promesoft/KicadJE_uP_DAC/RevA/KicadJE_uP_DAC_Top3.png

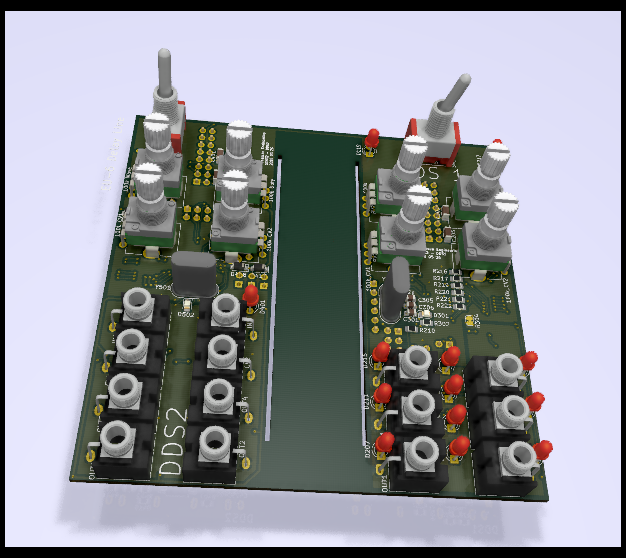
RevA/KicadJE_uP_DAC_Top3.png
